BwanaFr/heating-controller/software/Firmware/src/ntc.h

#ifndef _NTC_H_
#define _NTC_H_

#include <cstdint>

typedef struct NTC_VAL{
    double temperature;
    double resistance;
}NTC_VAL;

static const uint32_t ntc_vals_size = 206;
static const NTC_VAL ntc_vals[ntc_vals_size] = {
    {-55 ,53400},
    {-54 ,50100},
    {-53 ,47020},
    {-52 ,44160},
    {-51 ,41480},
    {-50 ,38990},
    {-49 ,36660},
    {-48 ,34480},
    {-47 ,32450},
    {-46 ,30550},
    {-45 ,28770},
    {-44 ,27110},
    {-43 ,25550},
    {-42 ,24090},
    {-41 ,22730},
    {-40 ,21450},
    {-39 ,20250},
    {-38 ,19130},
    {-37 ,18070},
    {-36 ,17080},
    {-35 ,16150},
    {-34 ,15280},
    {-33 ,14460},
    {-32 ,13680},
    {-31 ,12960},
    {-30 ,12270},
    {-29 ,11630},
    {-28 ,11030},
    {-27 ,10460},
    {-26 ,9918},
    {-25 ,9411},
    {-24 ,8934},
    {-23 ,8483},
    {-22 ,8058},
    {-21 ,7657},
    {-20 ,7278},
    {-19 ,6920},
    {-18 ,6582},
    {-17 ,6263},
    {-16 ,5960},
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
};


#endif
