BwanaFr/heating-controller/software/Firmware/src/system.cpp

#include "system.h"
#include "esp32s3/rom/rtc.h"

const char* get_reset_reason(int reason)
{
  switch ( reason)
  {
    case 1 : return "POWERON_RESET"; break;          /**<1,  Vbat power on reset*/
    case 3 : return "SW_RESET" ;break;               /**<3,  Software reset digital core*/
    case 4 : return "OWDT_RESET"; break;             /**<4,  Legacy watch dog reset digital core*/
    case 5 : return "DEEPSLEEP_RESET"; break;        /**<5,  Deep Sleep reset digital core*/
    case 6 : return "SDIO_RESET"; break;             /**<6,  Reset by SLC module, reset digital core*/
    case 7 : return "TG0WDT_SYS_RESET"; break;       /**<7,  Timer Group0 Watch dog reset digital core*/
    case 8 : return "TG1WDT_SYS_RESET"; break;       /**<8,  Timer Group1 Watch dog reset digital core*/
    case 9 : return "RTCWDT_SYS_RESET"; break;       /**<9,  RTC Watch dog Reset digital core*/
    case 10 : return "INTRUSION_RESET"; break;       /**<10, Instrusion tested to reset CPU*/
    case 11 : return "TGWDT_CPU_RESET"; break;       /**<11, Time Group reset CPU*/
    case 12 : return "SW_CPU_RESET"; break;          /**<12, Software reset CPU*/
    case 13 : return "RTCWDT_CPU_RESET"; break;      /**<13, RTC Watch dog Reset CPU*/
    case 14 : return "EXT_CPU_RESET"; break;         /**<14, for APP CPU, reseted by PRO CPU*/
    case 15 : return "RTCWDT_BROWN_OUT_RESET"; break;/**<15, Reset when the vdd voltage is not stable*/
    case 16 : return "RTCWDT_RTC_RESET"; break;      /**<16, RTC Watch dog reset digital core and rtc module*/
    default : return "NO_MEAN";
  }
}


const char* get_cpu0_reset_reason()
{
    return get_reset_reason(rtc_get_reset_reason(0));
}

const char* get_cpu1_reset_reason()
{
    return get_reset_reason(rtc_get_reset_reason(1));
}
