BwanaFr/heating-controller/software/Firmware/src/global_info.h

#ifndef _GLOBAL_INFO_H_
#define _GLOBAL_INFO_H_

/**
 * Gets and refresh network info
 * by sending proper LVGL events
*/
void refresh_network_info(void);

/**
 * Gets and refresh I/O info
 * by sending proper LVGL event
*/
void refresh_io_info(void);

#endif
