BwanaFr/heating-controller/software/Firmware/src/ui/ui.cpp

#include "ui.h"

#include "lvgl.h"
#include "home.h"
#include "setup.h"
#include "events.h"
#include "more.h"
#include "startup.h"

static lv_obj_t * prevScreen = NULL;

void ui_init(void)
{
    lv_disp_t * dispp = lv_disp_get_default();
    lv_theme_t * theme = lv_theme_default_init(dispp, lv_palette_main(LV_PALETTE_BLUE), lv_palette_main(LV_PALETTE_RED),
                                               true, LV_FONT_DEFAULT);
    lv_disp_set_theme(dispp, theme);    
    ui_Home_screen_init();
    ui_More_screen_init();
    ui_Setup_screen_init();
#ifndef SIMULATOR
    ui_Startup_screen_init();
    lv_disp_load_scr(ui_Startup);
#else
    lv_disp_load_scr(ui_Home);
#endif
}

/**
 * Shows home screen
*/
void ui_show_home(void)
{
    if(lv_scr_act() != ui_get_Home_screen())
        lv_scr_load_anim(ui_get_Home_screen(), LV_SCR_LOAD_ANIM_FADE_IN, 500, 0, false);
}

/**
 * Shows the setup screen
*/
void ui_show_setup(void)
{
    lv_scr_load_anim(ui_get_Setup_screen(), LV_SCR_LOAD_ANIM_FADE_IN, 500, 0, false);
}

/**
 * Shows the more screen
*/
void ui_show_more(void)
{
    lv_scr_load_anim(ui_get_More_screen(), LV_SCR_LOAD_ANIM_FADE_IN, 500, 0, false);
}
