BwanaFr/heating-controller/software/Firmware/src/ui/ui.h

#ifndef _UI_H
#define _UI_H

#include "lvgl.h"
#include "events.h"

/**
 * UI initialization 
*/
void ui_init(void);

/**
 * Shows home screen
*/
void ui_show_home(void);

/**
 * Shows the setup screen
*/
void ui_show_setup(void);

/**
 * Shows the more screen
*/
void ui_show_more(void);

#endif
