BwanaFr/heating-controller/software/Firmware/src/ui/ui_utils.h

#ifndef _UI_UTILS_H_
#define _UI_UTILS_H_

#include "lvgl.h"

/**
 * Updates label text
*/
template <typename T>
void update_label_cb(lv_event_t *e){
    lv_obj_t *label = lv_event_get_target(e);
    lv_msg_t *m = lv_event_get_msg(e);
    lv_obj_t *parent = (lv_obj_t *)lv_event_get_user_data(e);

    const char *fmt = (const char *)lv_msg_get_user_data(m);
    const T *v = (const T *)lv_msg_get_payload(m);
    if(v == nullptr){
        lv_obj_add_flag(label, LV_OBJ_FLAG_HIDDEN);
        if(parent)
            lv_obj_add_flag(parent, LV_OBJ_FLAG_HIDDEN);
    }else{
        lv_obj_clear_flag(label, LV_OBJ_FLAG_HIDDEN);
        if(parent)
            lv_obj_clear_flag(parent, LV_OBJ_FLAG_HIDDEN);
        lv_label_set_text_fmt(label, fmt, *v);
    }
}

/**
 * Specialization for the string
*/
template <>
void update_label_cb<const char *>(lv_event_t *e);

/**
 * Specialization for the Temperature
*/
template <>
void update_label_cb<double>(lv_event_t *e);

/**
    Create an labeled display
**/
lv_obj_t * create_labeled_display(lv_obj_t * parent, const char* text, lv_obj_t*(*constructor)(lv_obj_t *));

/**
    Create an info display
**/
template <typename T>
lv_obj_t * create_info_display(lv_obj_t * parent, const char* text, const char* format, uint32_t msg_id, bool hideParent=false)
{
    lv_obj_t * valLabel = create_labeled_display(parent, text, lv_label_create);
    lv_obj_set_width(valLabel, LV_SIZE_CONTENT);
    lv_obj_set_height(valLabel, LV_SIZE_CONTENT);
    lv_label_set_text(valLabel, "???");
    lv_obj_set_style_text_color(valLabel, lv_palette_main(LV_PALETTE_LIGHT_BLUE), 0);
    lv_obj_set_style_pad_right(valLabel, LV_DPX(10), LV_PART_MAIN);
    lv_obj_add_event_cb(valLabel, update_label_cb<T>, LV_EVENT_MSG_RECEIVED, hideParent ? lv_obj_get_parent(valLabel) : NULL);
    lv_msg_subsribe_obj(msg_id, valLabel, (void *)format);
    return valLabel;
}

/**
    Create an info display
**/
template <typename T>
lv_obj_t * create_info_display(lv_obj_t * parent, const char* text, const char* format, T value)
{
    lv_obj_t * valLabel = create_labeled_display(parent, text, lv_label_create);
    lv_obj_set_width(valLabel, LV_SIZE_CONTENT);
    lv_obj_set_height(valLabel, LV_SIZE_CONTENT);
    lv_label_set_text_fmt(valLabel, format, value);
    lv_obj_set_style_text_color(valLabel, lv_palette_main(LV_PALETTE_LIGHT_BLUE), 0);
    lv_obj_set_style_pad_right(valLabel, LV_DPX(10), LV_PART_MAIN);
    return valLabel;
}


#endif
